ms02-1337/OpenDyno/DynoLogic/Hardware/_lib/5pinConnector/1725685.stp

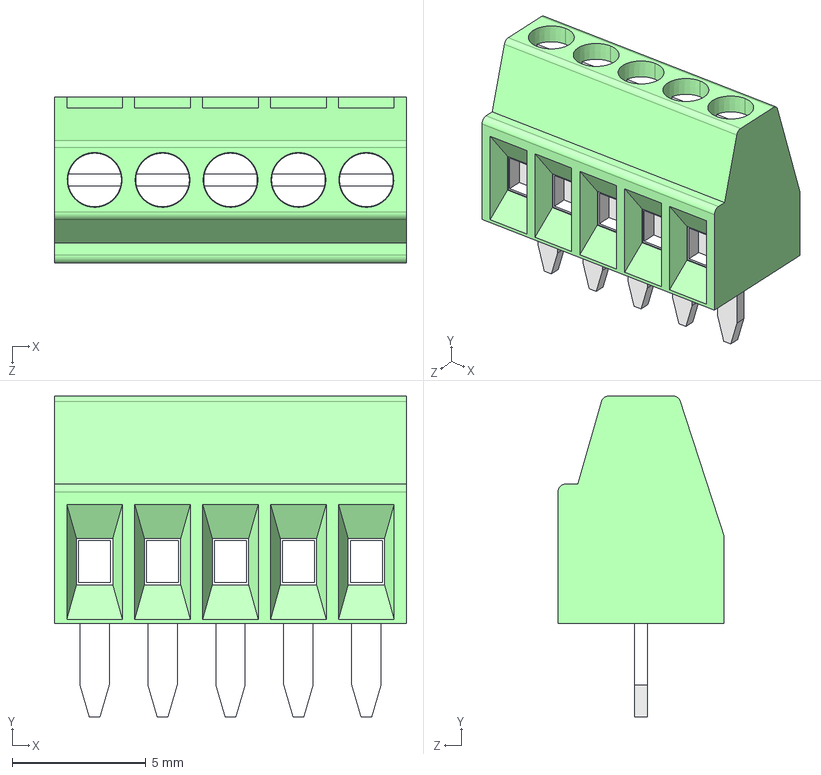
[picture p20: CAD file, 2026-06-18]
DynoLogic/Hardware/_lib/5pinConnector/1725685.stp
13.2 x 12.0 x 6.20 mm
LPattern6[2]_1.stp
Boss-Extrude9_1.stp
Cut-Extrude11_1.stp
LPattern6[3]_1.stp
LPattern6[4]_1.stp
LPattern6[1]_1.stp
