ms02-1337/OpenDyno/DynoLogic/Hardware/_lib/B82442T1683K050/B82442T1683K050.stp

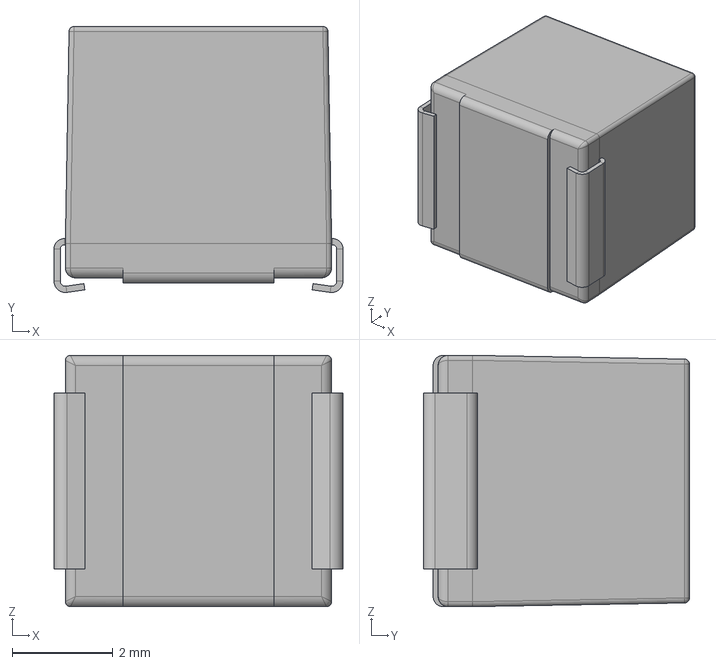
[picture p21: CAD file, 2026-06-18]
DynoLogic/Hardware/_lib/B82442T1683K050/B82442T1683K050.stp
5.75 x 5.29 x 5.00 mm
