ms02-1337/OpenDyno/DynoLogic/Hardware/_lib/DMKDS/1740000.stp

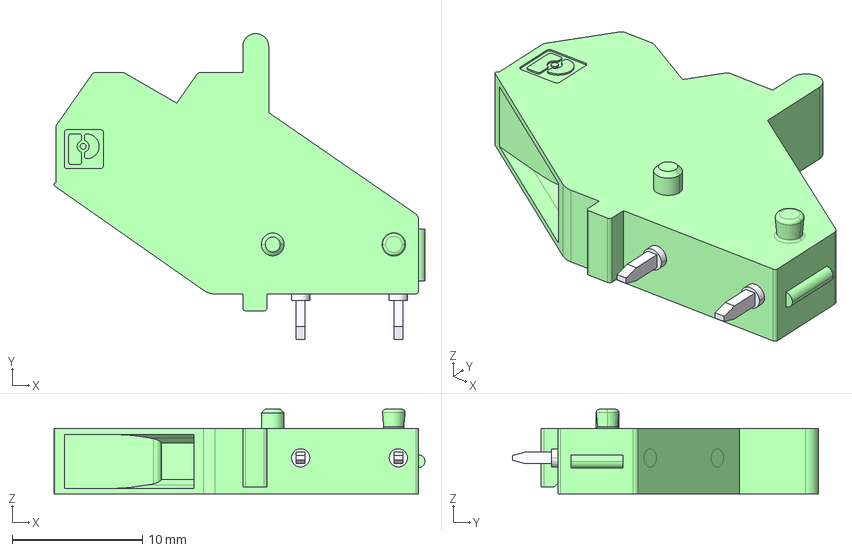
[picture p22: CAD file, 2026-06-18]
DynoLogic/Hardware/_lib/DMKDS/1740000.stp
28.5 x 23.5 x 6.50 mm
