ms02-1337/OpenDyno/DynoLogic/Hardware/_lib/MAX22530AWE/MAX22530AWE+T.stp

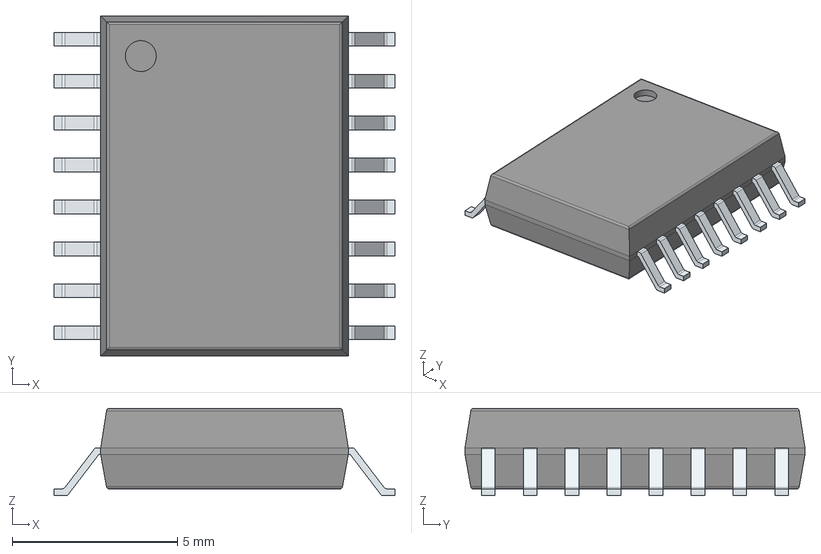
[picture p23: CAD file, 2026-06-18]
DynoLogic/Hardware/_lib/MAX22530AWE/MAX22530AWE+T.stp
10.3 x 10.3 x 2.65 mm
PinsArrayLR
