ms02-1337/OpenDyno/DynoServer/app/services/can_ids.py

# RX IDs - Microcontroller to Server (Telemetry)

CAN_LIVE_SPEED_ID = 0x01
CAN_STATUS_ID = 0x02
CAN_REQUEST_CONFIG_ID = 0x03
CAN_ELECTRICAL_CURRENT_ID = 0x04
CAN_ELECTRICAL_VOLTAGE_ID = 0x05
CAN_MICRO_HEARTBEAT_ID = 0x06
CAN_ENV_ID = 0x07
CAN_DEBUG_LIVE_ID = 0x08
CAN_ACC_ID = 0x09
CAN_BRAKE_TEMPERATURE = 0x10
CAN_ACC_DEBUG_ID = 0x11
CAN_LIVE_SPEED_TORQUE_DEBUG_ID = 0x12
CAN_DS18B20_TEMP_ID = 0x13

# TX IDs - Server to Microcontroller (Commands)

RUN_MODE_ID = 0x100
INSTRUCTION_ID = 0x101
APP_HEARTBEAT_ID = 0x102
CHECKSUM_ID = 0x103
DEBUG_CONFIG_ID = 0x104
ENABLE_LIVE_ID = 0x105
SET_PWM_VALUE = 0x106
TARE_LOAD_CELL_ID = 0x107
TORQUE_KP_CONFIG_ID = 0x109
TORQUE_KI_CONFIG_ID = 0x110
TORQUE_KD_CONFIG_ID = 0x111
SPEED_KP_CONFIG_ID = 0x112
SPEED_KI_CONFIG_ID = 0x113
SPEED_KD_CONFIG_ID = 0x114
DYNAMIC_KP_CONFIG_ID = 0x115
DYNAMIC_KI_CONFIG_ID = 0x116
DYNAMIC_KD_CONFIG_ID = 0x117
LOAD_CELL_CONFIG_1_ID = 0x118
PWM_CONFIG_ID = 0x119
LOW_PASS_FILTERS_ID = 0x120
SPEED_LIMITS_ID = 0x121
DYNAMIC_CONFIG_1_ID = 0x122
DYNAMIC_CONFIG_2_ID = 0x123
DYNAMIC_CONFIG_3_ID = 0x124
DYNAMIC_CONFIG_4_ID = 0x125
LOAD_CELL_CONFIG_2_ID = 0x126
